landen-points/analogcomputer/kicad/analogcomputer-v1.kicad_sch

## KiCad design kicad/analogcomputer-v1.kicad_sch (2025-04-17)

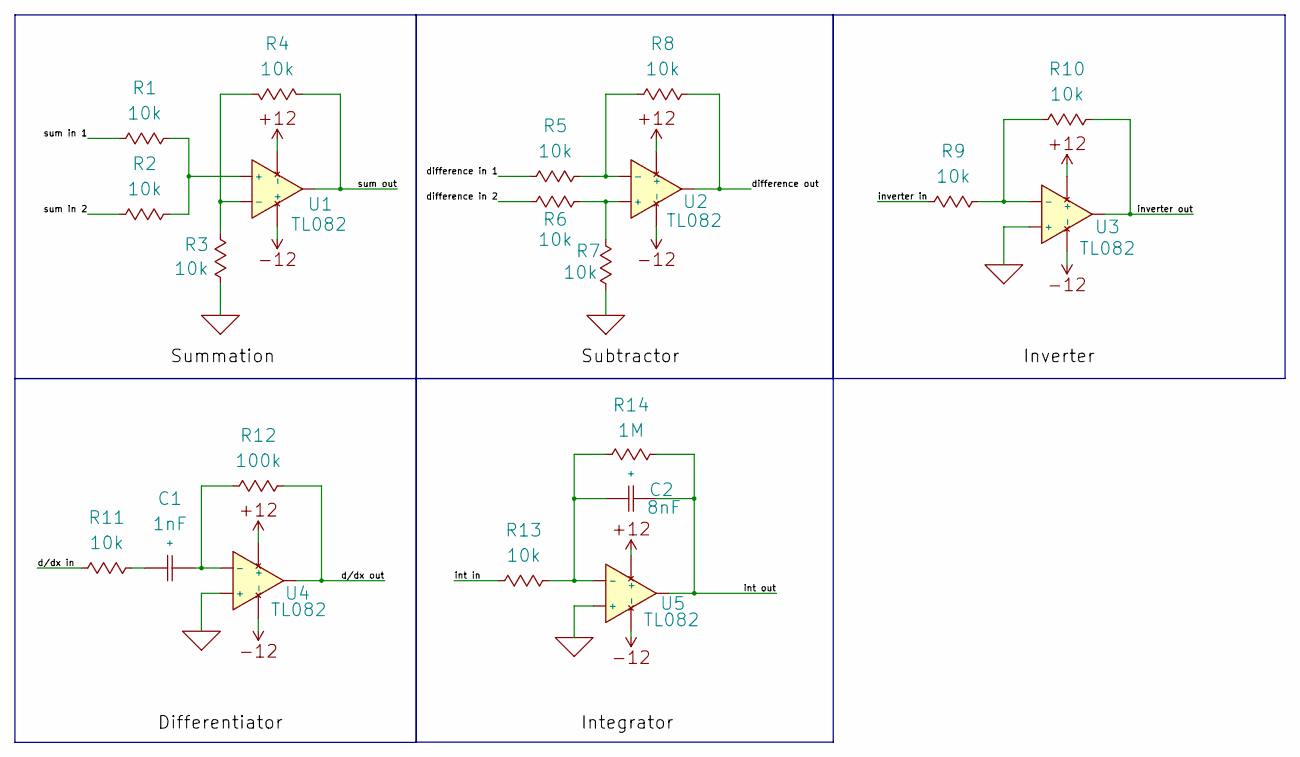
[picture p6: schematic analogcomputer-v1.kicad_sch]

Parts:
C1: 1nF
C2: 8nF
R1, R2, R3, R4, R5, R6, R7, R8, R9, R10, R11, R13: 10k
R12: 100k
R14: 1M
U1, U2, U3, U4, U5: TL082

Connections:
unnamed: C1.1 (+), R11.2 (-)
unnamed: C1.2 (-), R12.1 (+), U4.2 (-)
unnamed: C2.2 (-), R13.2 (-), R14.1 (+), U5.2 (-)
unnamed: R1.2 (-), R2.2 (-), U1.1 (+)
unnamed: R3.1 (+), R4.2 (-), U1.2 (-)
unnamed: R5.2 (-), R8.1 (+), U2.2 (-)
unnamed: R6.1 (+), R7.1 (+), U2.1 (+)
unnamed: R9.2 (-), R10.1 (+), U3.2 (-)
P,+12: U1.4 (-), U2.3 (+), U3.3 (+), U4.3 (+), U5.3 (+)
P,-12: U1.3 (+), U2.4 (-), U3.4 (-), U4.4 (-), U5.4 (-)
P,GND: R3.2 (-), R7.2 (-), U3.1 (+), U4.1 (+), U5.1 (+)
difference in 1: R5.1 (+)
difference in 2: R6.2 (-)
difference out: R8.2 (-), U2.5 (OUT)
d/dx in: R11.1 (+)
d/dx out: R12.2 (-), U4.5 (OUT)
int in: R13.1 (+)
int out: C2.1 (+), R14.2 (-), U5.5 (OUT)
inverter in: R9.1 (+)
inverter out: R10.2 (-), U3.5 (OUT)
sum in 1: R1.1 (+)
sum in 2: R2.1 (+)
sum out: R4.1 (+), U1.5 (OUT)
